123UsernamemanresU321/CSP/CAD/Cover_Plate_Reference.dxf

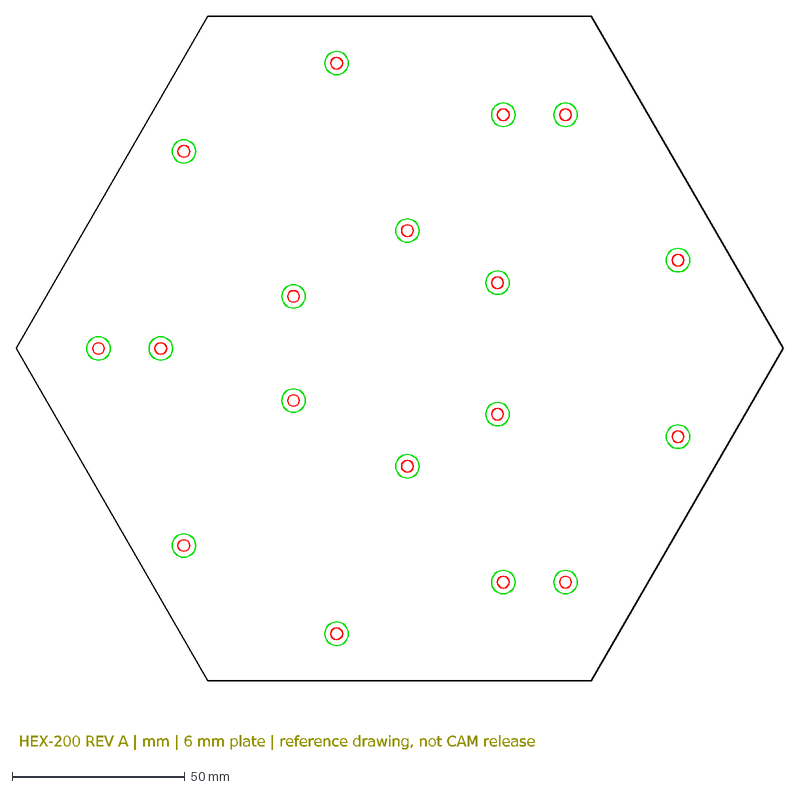
[picture p19: CAD file, 2026-09-23]
CAD/Cover_Plate_Reference.dxf
HEX-200 REV A | mm | 6 mm plate | reference drawing, not CAM release
