123UsernamemanresU321/CSP/CAD/E01.step

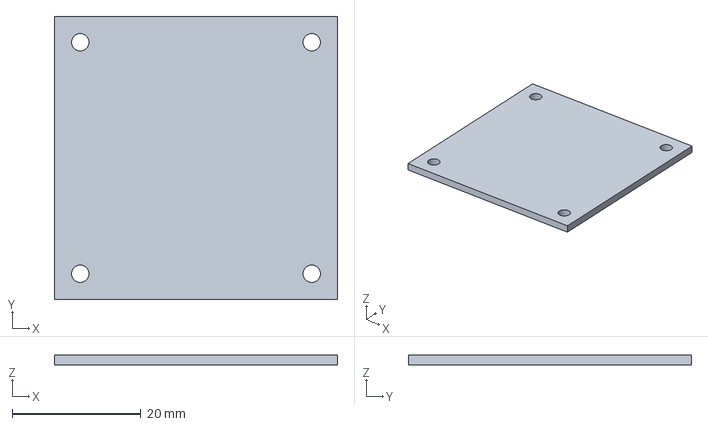
[picture p20: CAD file, 2026-09-23]
CAD/E01.step
44.0 x 44.0 x 1.60 mm
