123UsernamemanresU321/CSP/meshes/S01_1.stl

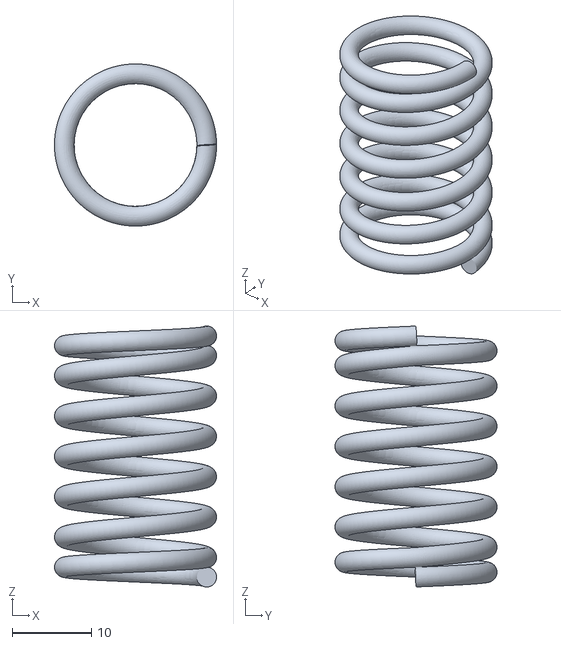
[picture p21: CAD file, 2026-09-23]
meshes/S01_1.stl
20.5 x 20.5 x 33.0
