123UsernamemanresU321/CSP/meshes/G02_1.stl

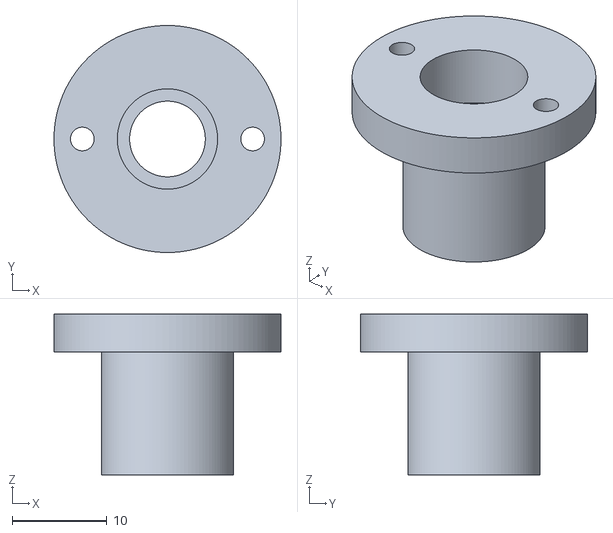
[picture p22: CAD file, 2026-09-23]
meshes/G02_1.stl
24.0 x 24.0 x 17.0
