123UsernamemanresU321/CSP/CAD/G03_1.step

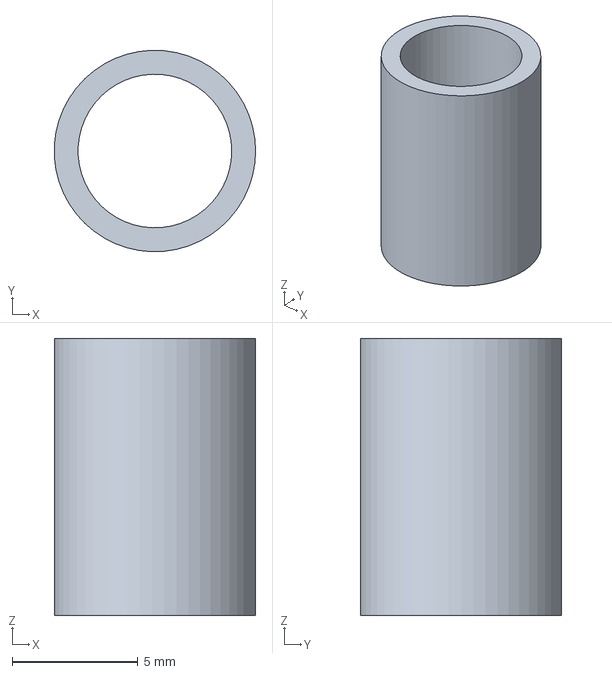
[picture p23: CAD file, 2026-09-23]
CAD/G03_1.step
7.99 x 8.00 x 11.0 mm
