123UsernamemanresU321/CSP/CAD/A01.step

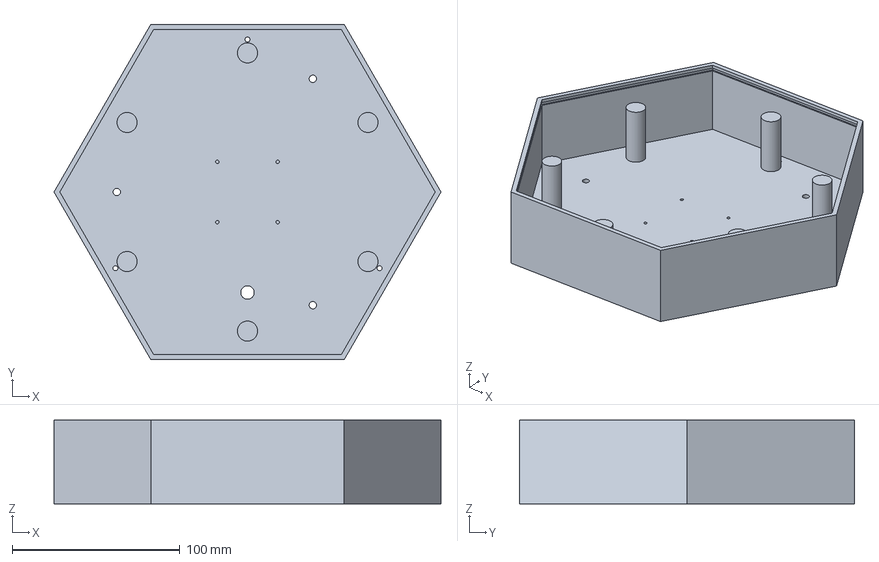
[picture p24: CAD file, 2026-09-23]
CAD/A01.step
230.9 x 200.0 x 50.0 mm
